paulmartinezcuenta/UltiCore-V1-PLC/RESULTS/9.jpeg

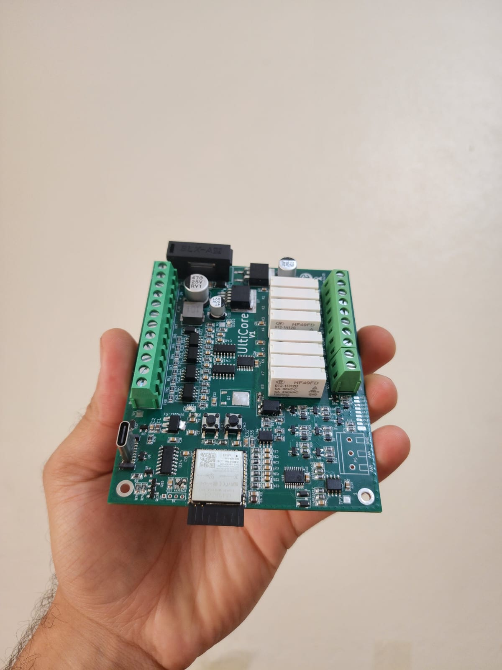
RESULTS/9.jpeg
