paulmartinezcuenta/UltiCore-V1-PLC/RESULTS/1.jpeg

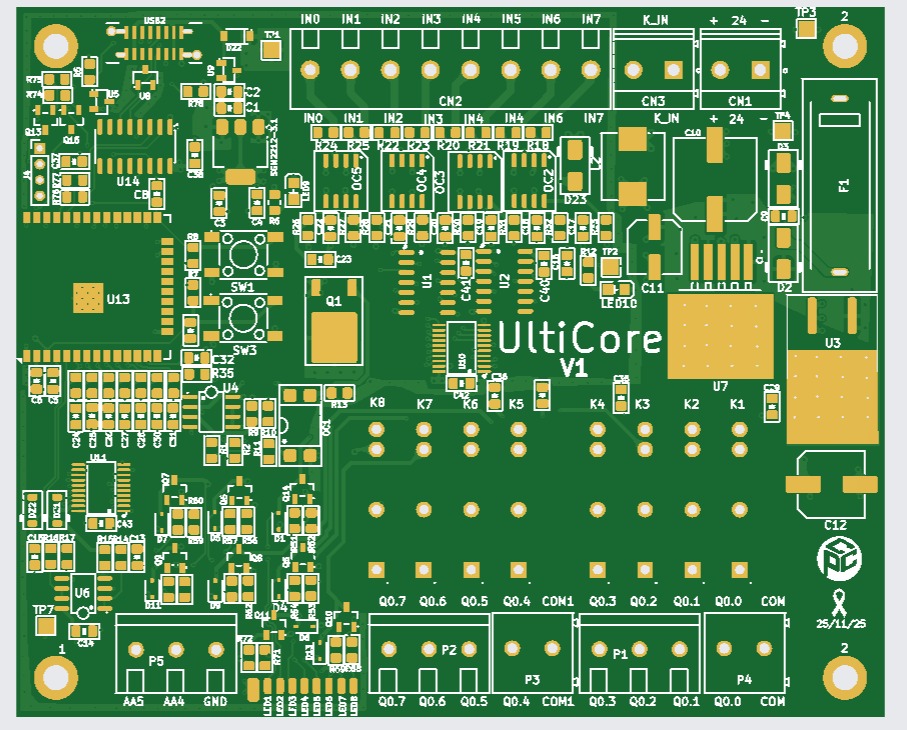
RESULTS/1.jpeg
