paulmartinezcuenta/UltiCore-V1-PLC/RESULTS/2.jpeg

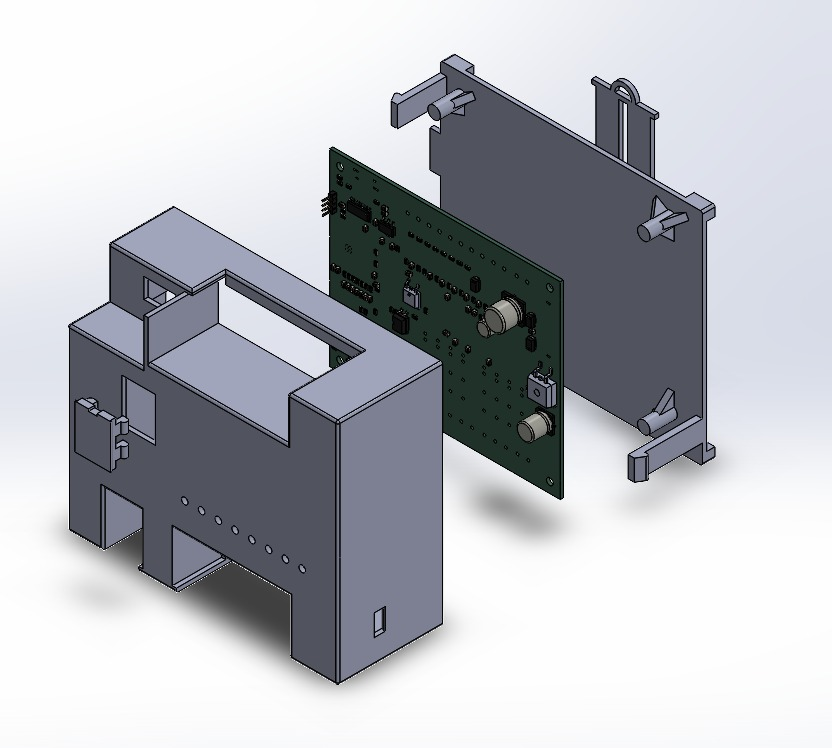
RESULTS/2.jpeg
