paulmartinezcuenta/UltiCore-V1-PLC/RESULTS/3.jpeg

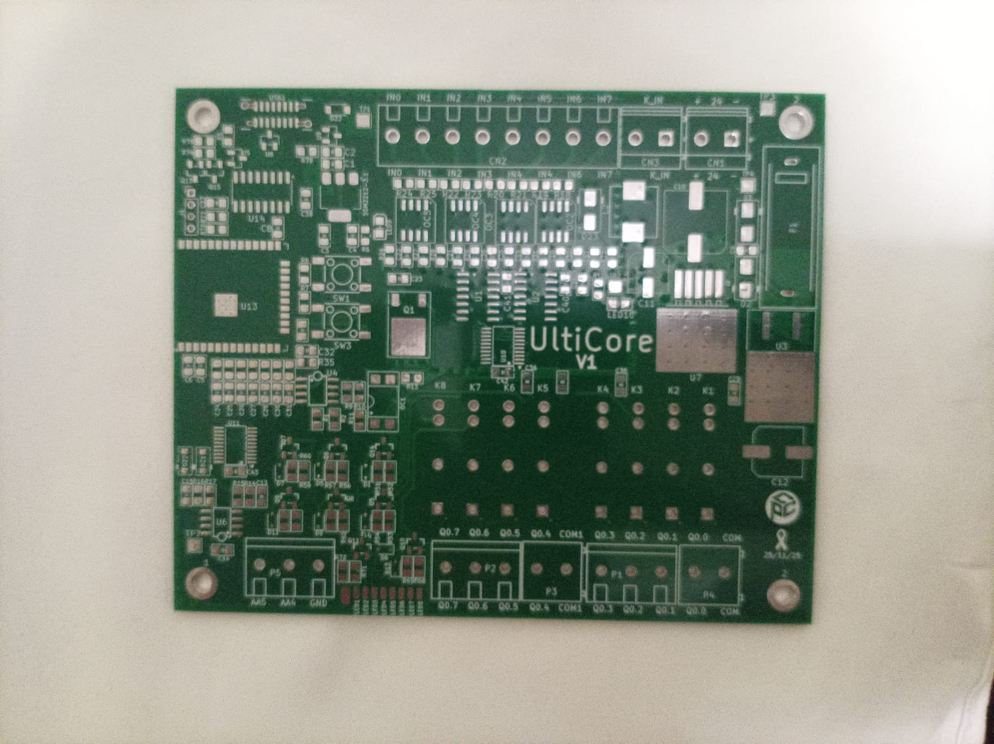
RESULTS/3.jpeg
