paulmartinezcuenta/UltiCore-V1-PLC/RESULTS/4.jpeg

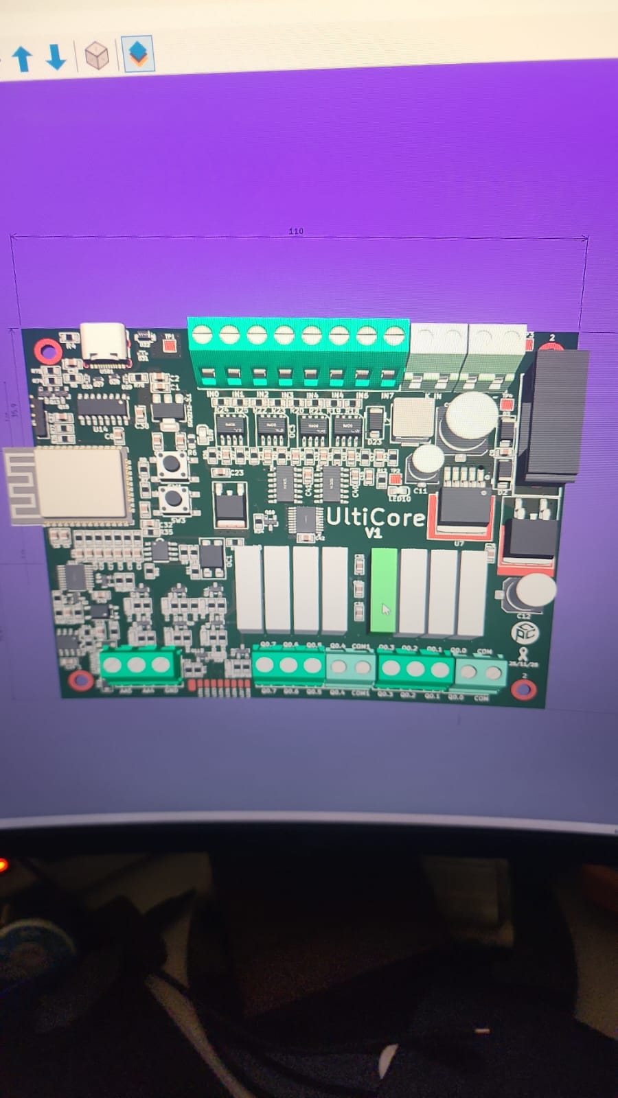
RESULTS/4.jpeg
