paulmartinezcuenta/UltiCore-V1-PLC/RESULTS/5.jpeg

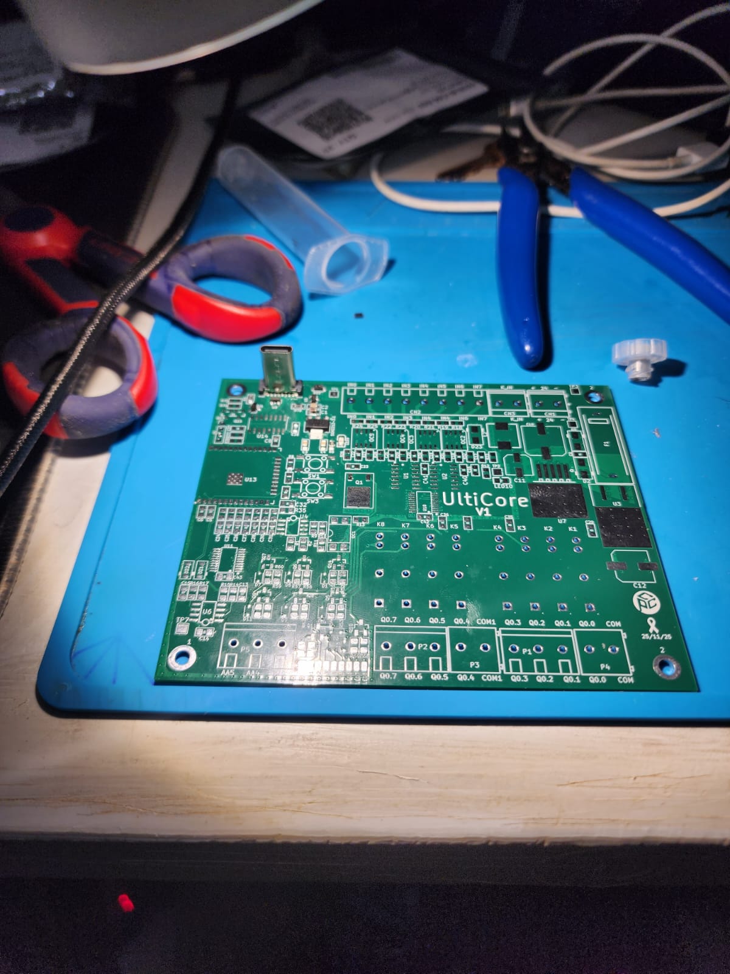
RESULTS/5.jpeg
