paulmartinezcuenta/UltiCore-V1-PLC/RESULTS/6.jpeg

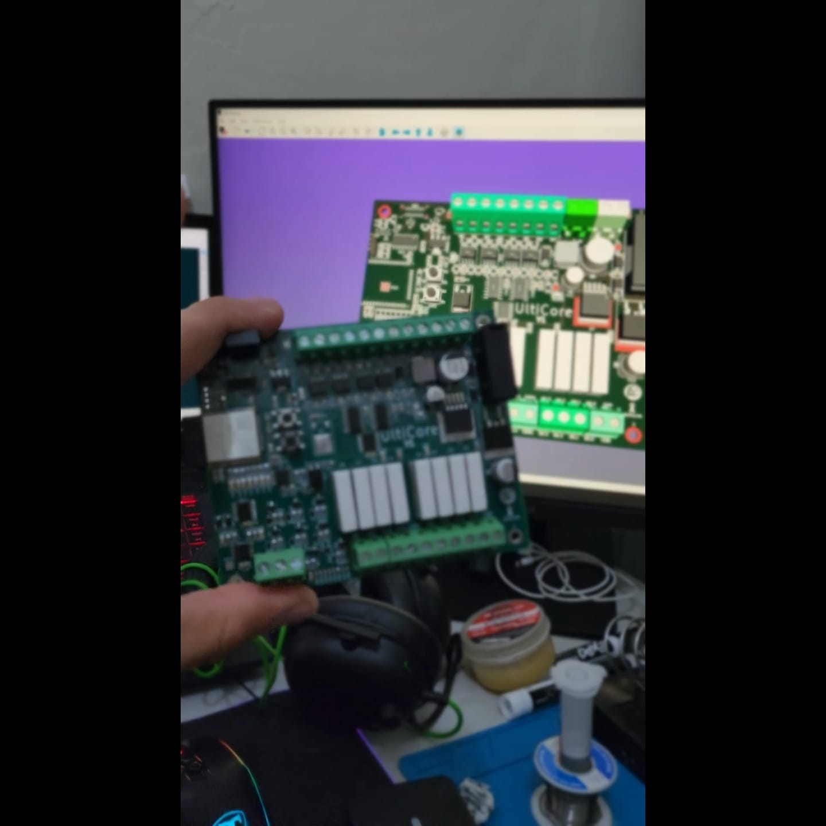
RESULTS/6.jpeg
