paulmartinezcuenta/UltiCore-V1-PLC/RESULTS/7.jpeg

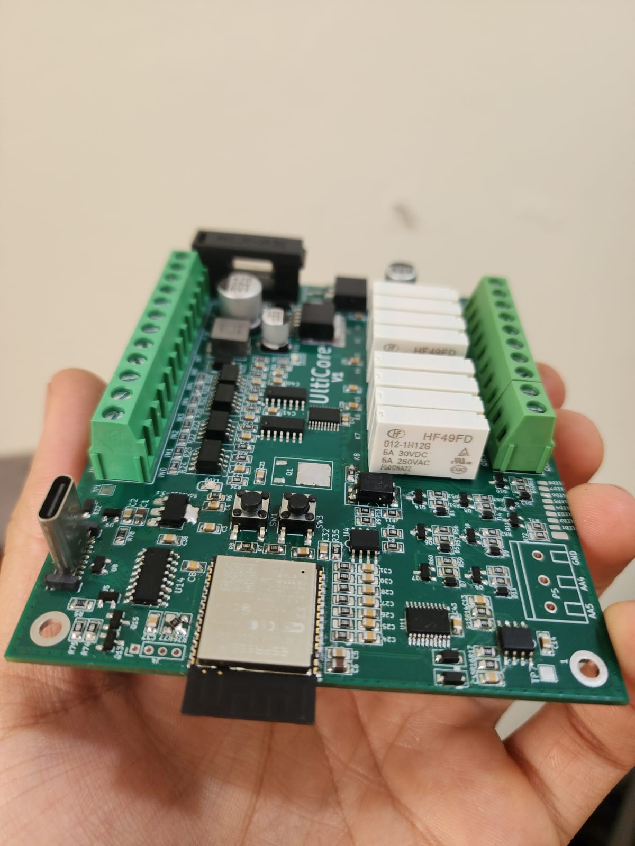
RESULTS/7.jpeg
