paulmartinezcuenta/UltiCore-V1-PLC/RESULTS/8.jpeg

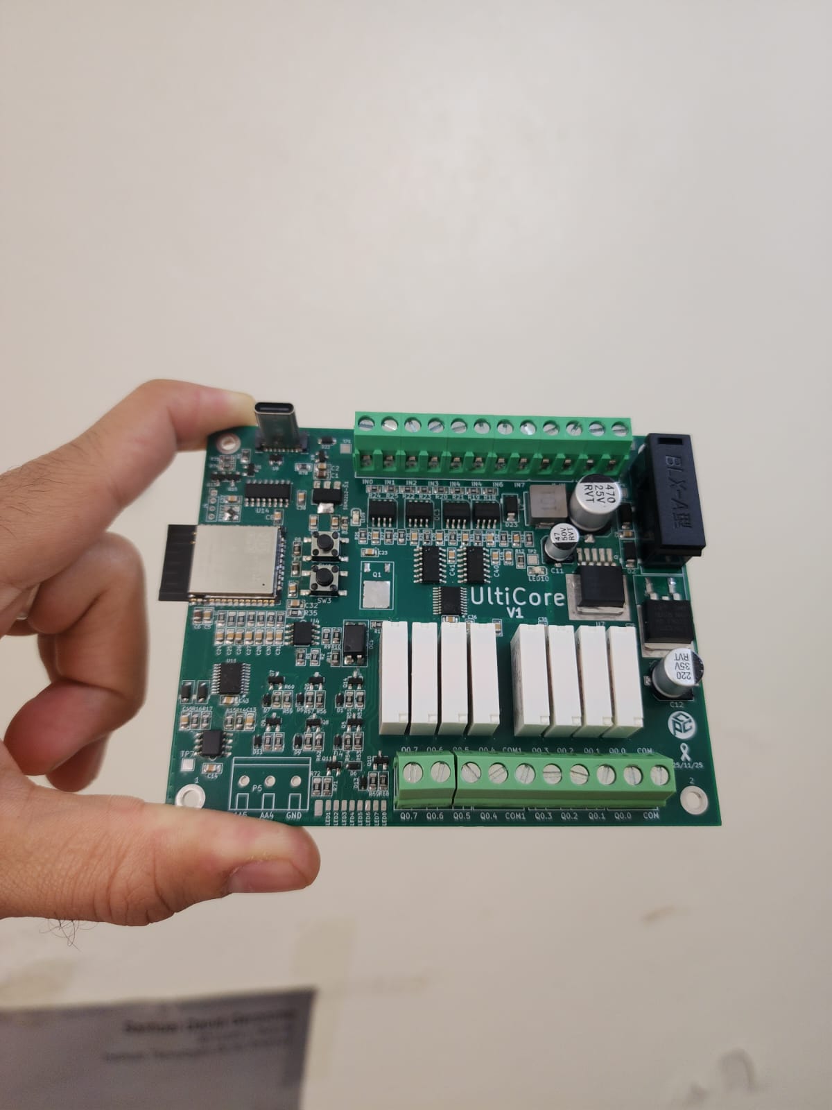
RESULTS/8.jpeg
