paulmartinezcuenta/UltiCore-V1-PLC/RESULTS/10.jpeg

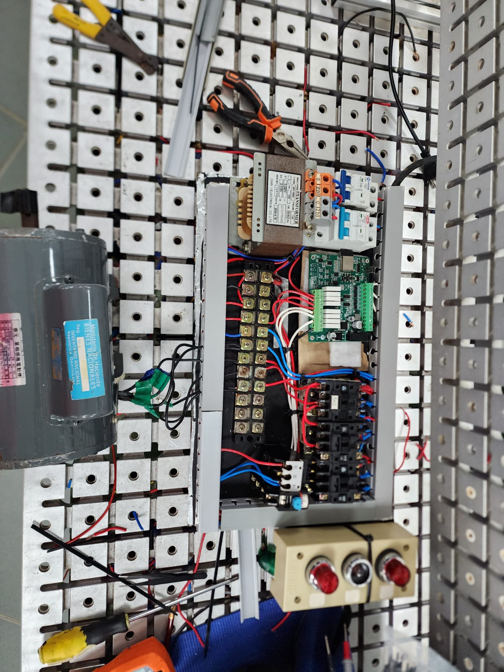
RESULTS/10.jpeg
